michael-betz/Espirgbani/pcb/pdf/2.png

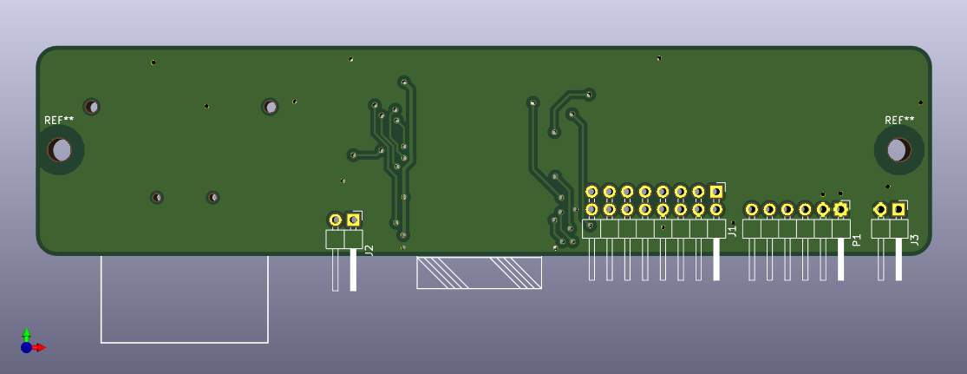
pcb/pdf/2.png
