michael-betz/Espirgbani/src/main/sdcard.h

#ifndef SDCARD_H
#define SDCARD_H

#define GPIO_SD_CLK  33
#define GPIO_SD_MOSI 32
#define GPIO_SD_MISO 12
#define GPIO_SD_CS   14

void initSd();

#endif
